Matheus-Souza-Rozendo/circuito-eletronico-para-carregamento-de-pilhas-de-litio/images/image9.png

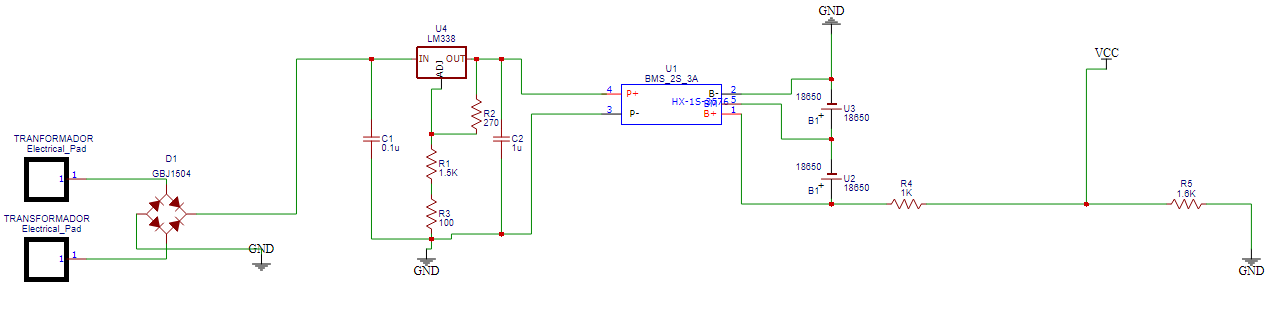
images/image9.png
